UCLcaozhiyu/Dissertation_book_marker/bookstander2/RC522/RC522.ino

#include <SPI.h>
#include <MFRC522.h>
#include <Wire.h>
#include <Adafruit_GFX.h>
#include <Adafruit_SSD1306.h>

#define SCREEN_WIDTH 128
#define SCREEN_HEIGHT 64
#define OLED_RESET    -1 // 通常不用
Adafruit_SSD1306 display(SCREEN_WIDTH, SCREEN_HEIGHT, &Wire, OLED_RESET);

// 绑定引脚：使用 C3 Super Mini 上的实际 GPIO
#define SS_PIN    7    // RC522 的 SDA 接 GPIO7
#define RST_PIN   10   // RC522 的 RST 接 GPIO10

MFRC522 mfrc522(SS_PIN, RST_PIN);

void setup() {
  Serial.begin(115200);
  delay(2000); // Wait for serial ready

  // OLED I2C init
  Wire.begin(9, 8); // SDA=9, SCL=8

  if(!display.begin(SSD1306_SWITCHCAPVCC, 0x3C)) {
    Serial.println(F("OLED init failed!"));
    for(;;);
  }
  display.clearDisplay();
  display.setTextSize(1);
  display.setTextColor(SSD1306_WHITE);
  display.setCursor(0,0);
  display.println("Place card to scan");
  display.display();

  Serial.println("OLED initialized.");

  SPI.begin(4, 5, 6);  // SCK=4, MISO=5, MOSI=6
  Serial.println("SPI initialized.");

  mfrc522.PCD_Init();
  Serial.println("RC522 ready. Place card to scan.");
}

void loop() {
  // Wait for a new card
  if (!mfrc522.PICC_IsNewCardPresent()) return;
  if (!mfrc522.PICC_ReadCardSerial()) return;

  Serial.print("Card UID: ");
  display.clearDisplay();
  display.setCursor(0,0);
  display.print("Card UID:");

  for (byte i = 0; i < mfrc522.uid.size; i++) {
    if (mfrc522.uid.uidByte[i] < 0x10) {
      Serial.print(" 0");
      display.print(" 0");
    } else {
      Serial.print(" ");
      display.print(" ");
    }
    Serial.print(mfrc522.uid.uidByte[i], HEX);
    display.print(mfrc522.uid.uidByte[i], HEX);
  }
  Serial.println();
  display.display();

  // Wait until card is removed
  Serial.println("Remove card to scan again.");
  display.setCursor(0, 16);
  display.print("Remove card...");
  display.display();
  while (mfrc522.PICC_IsNewCardPresent() || mfrc522.PICC_ReadCardSerial()) {
    delay(100);
  }
  Serial.println("Ready for next card.");
  display.clearDisplay();
  display.setCursor(0,0);
  display.print("Place card to scan");
  display.display();
}
